nicokorn/STM32F103_AudioSpectrumVisualizer/docs/20220124_210543.jpg

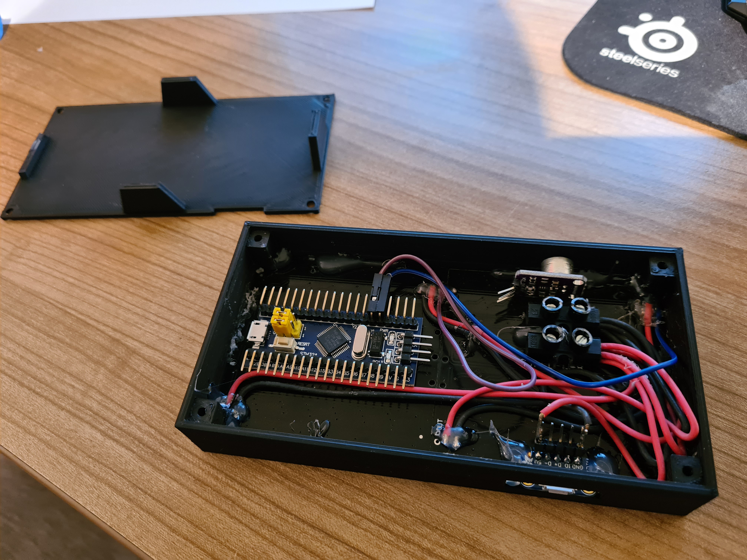
docs/20220124_210543.jpg
