nicokorn/STM32F103_AudioSpectrumVisualizer/docs/20220214_170019.jpg

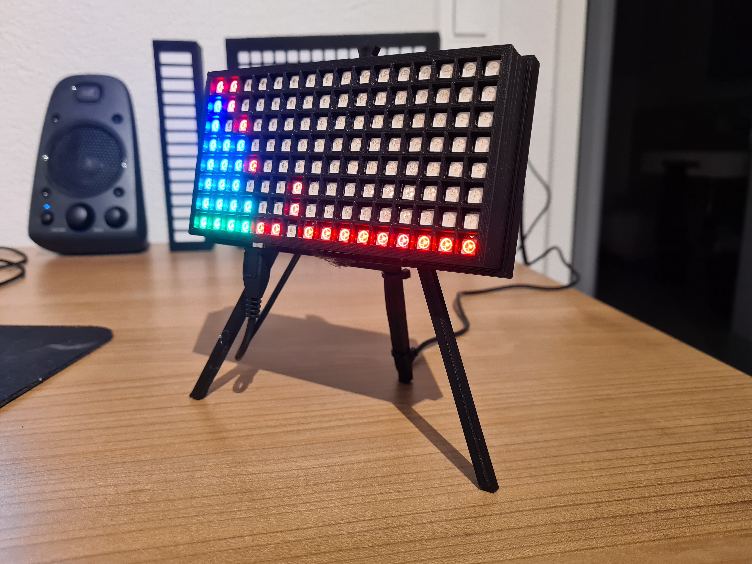
docs/20220214_170019.jpg
