nicokorn/STM32F103_AudioSpectrumVisualizer/docs/20220214_170028.jpg

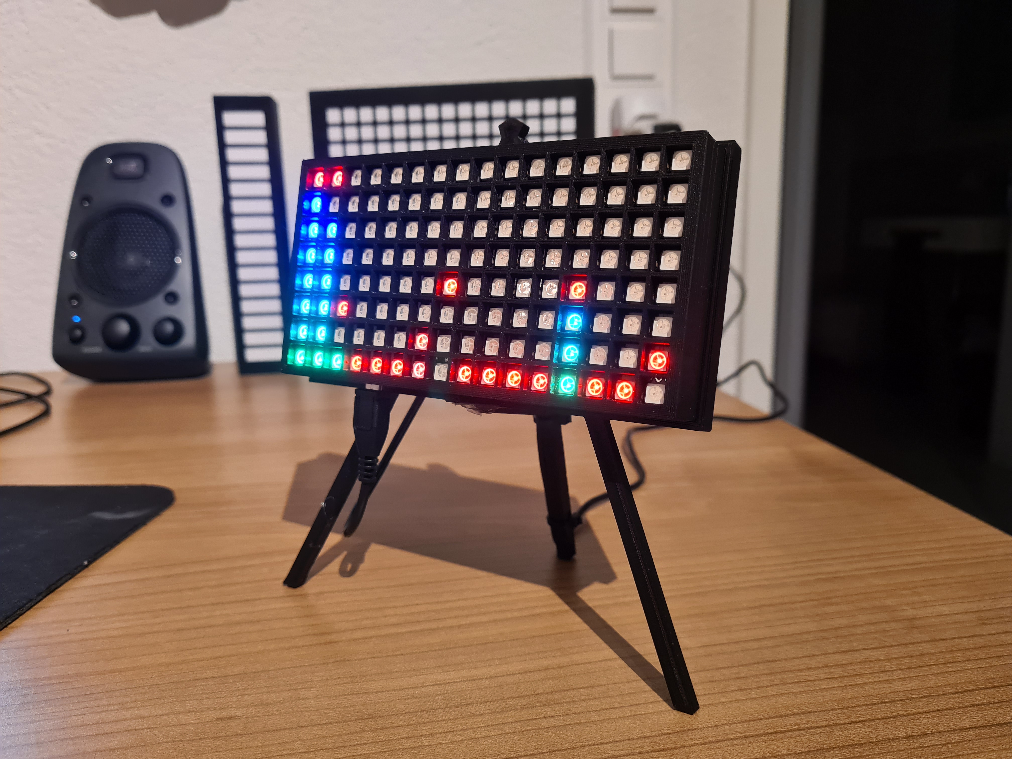
docs/20220214_170028.jpg
